hrickards/bioniscope/writeup/electronics.tex

\documentclass[12pt,a4paper]{report}

% Custom styles
\usepackage{electronics}

% Bibliography
\usepackage[citestyle=authortitle,url=true]{biblatex}
\addbibresource{electronics.bib}

\begin{document}

% Title page
\input{./tex/title.tex}

\tableofcontents
\listoffigures
%\listoftables

% Section A: Problem Analysis and Solution Design
\input{./tex/problem_analysis.tex}

% Section B: System Development
\input{./tex/system_development.tex}

% Section C: Making Measurements
\input{./tex/testing.tex}

% Section D: Evaluation and Reprot
\input{./tex/evaluation.tex}

\appendix
% Derivation of the fourier series of a square wave
\input{./tex/fourier_series_square_wave.tex}

% PIC Program Code
\input{./tex/pic_code.tex}

\listoffixmes

\printbibliography

\end{document}
