hrickards/bioniscope/circuit/alpha5/pcb_big.pdf

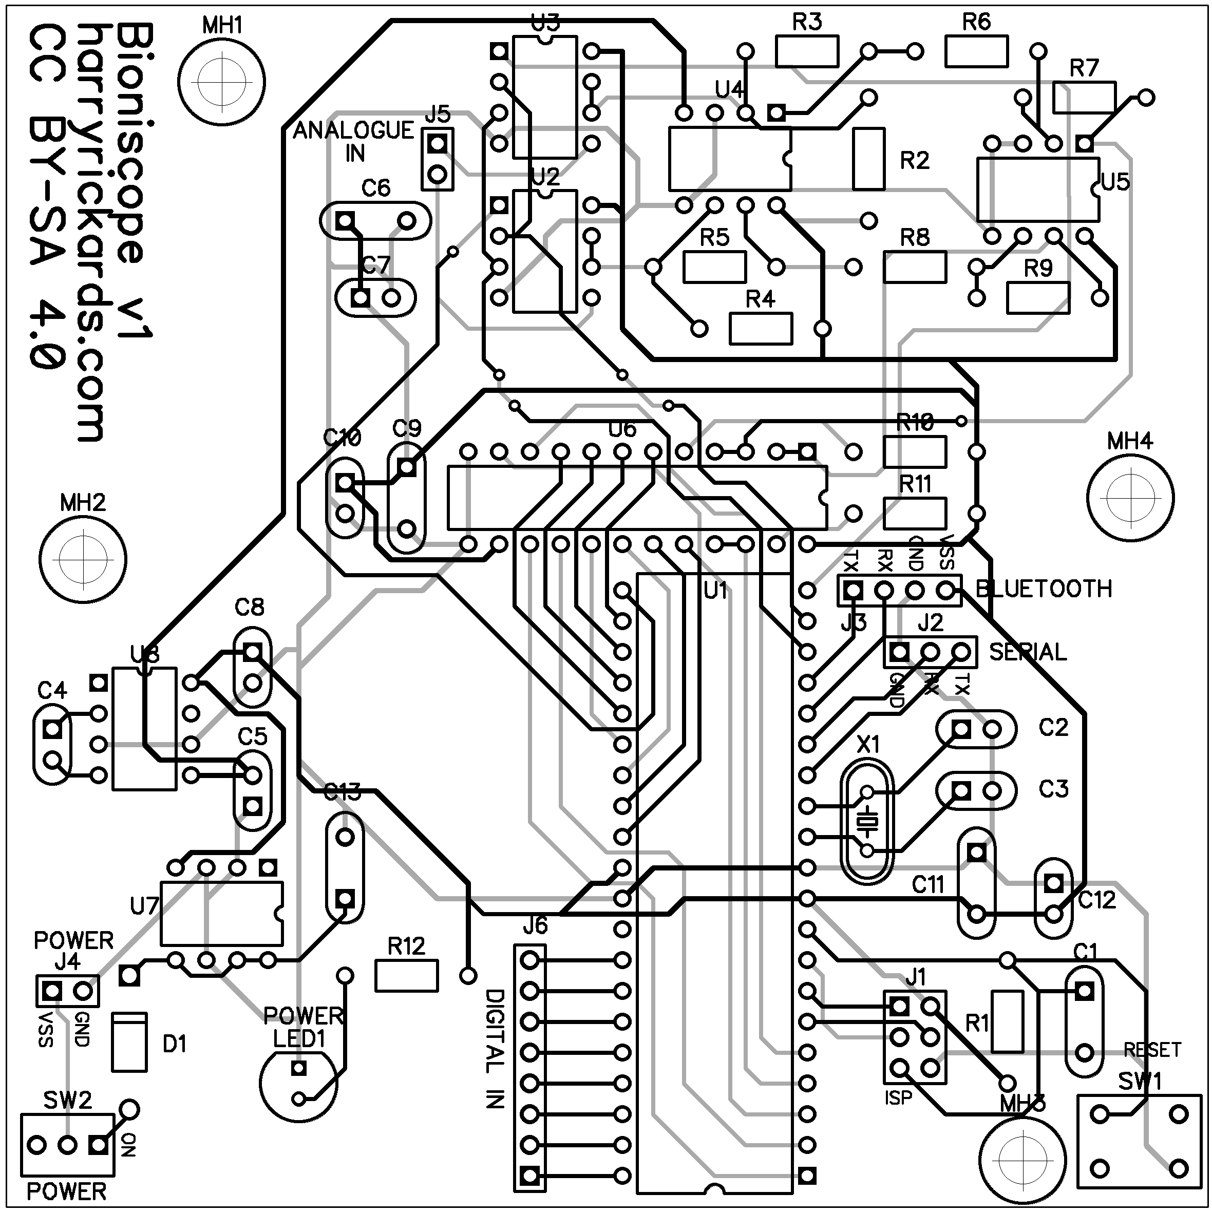
[picture p58: page 1]
