hrickards/bioniscope/writeup/img/pcb/analogue.pdf

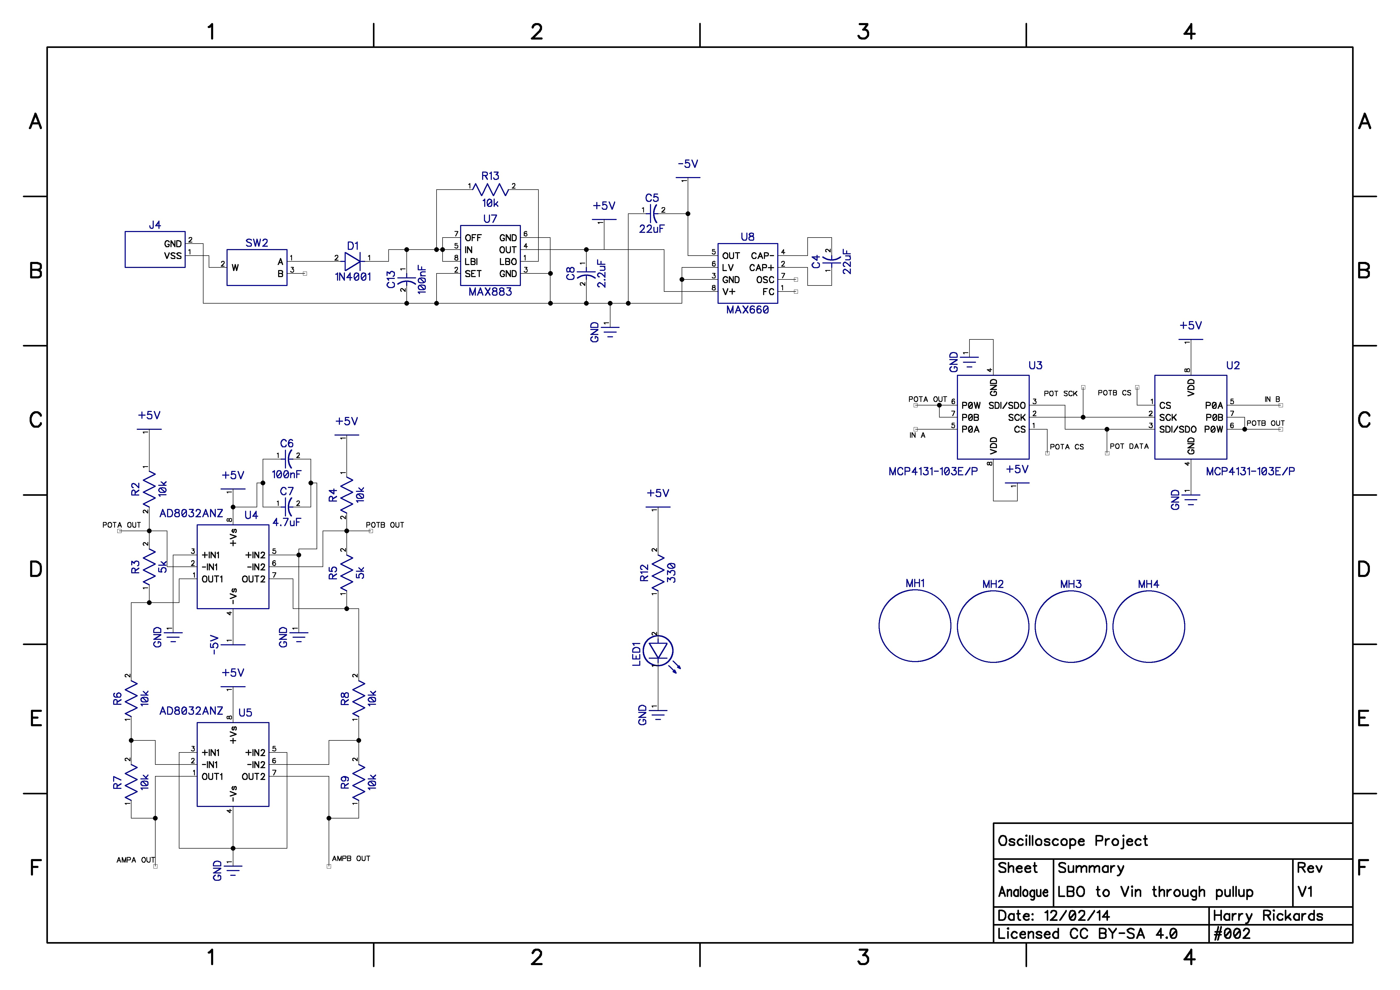
[picture p59: page 1]
