hrickards/bioniscope/writeup/img/pcb/digital.pdf

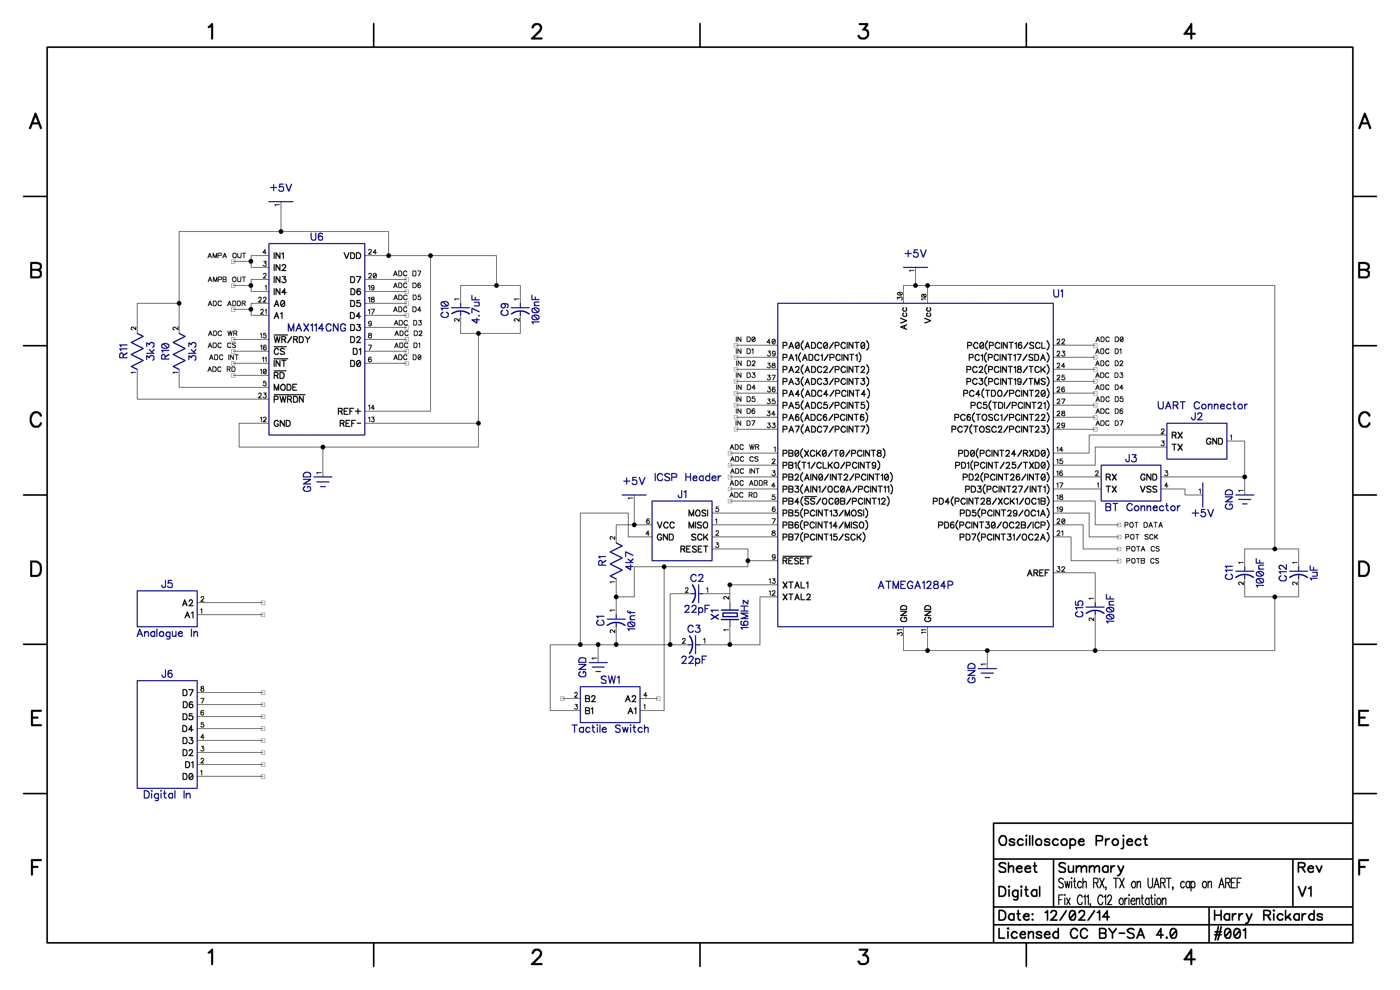
[picture p60: page 1]
