hrickards/bioniscope/circuit/alpha4/analogue.png

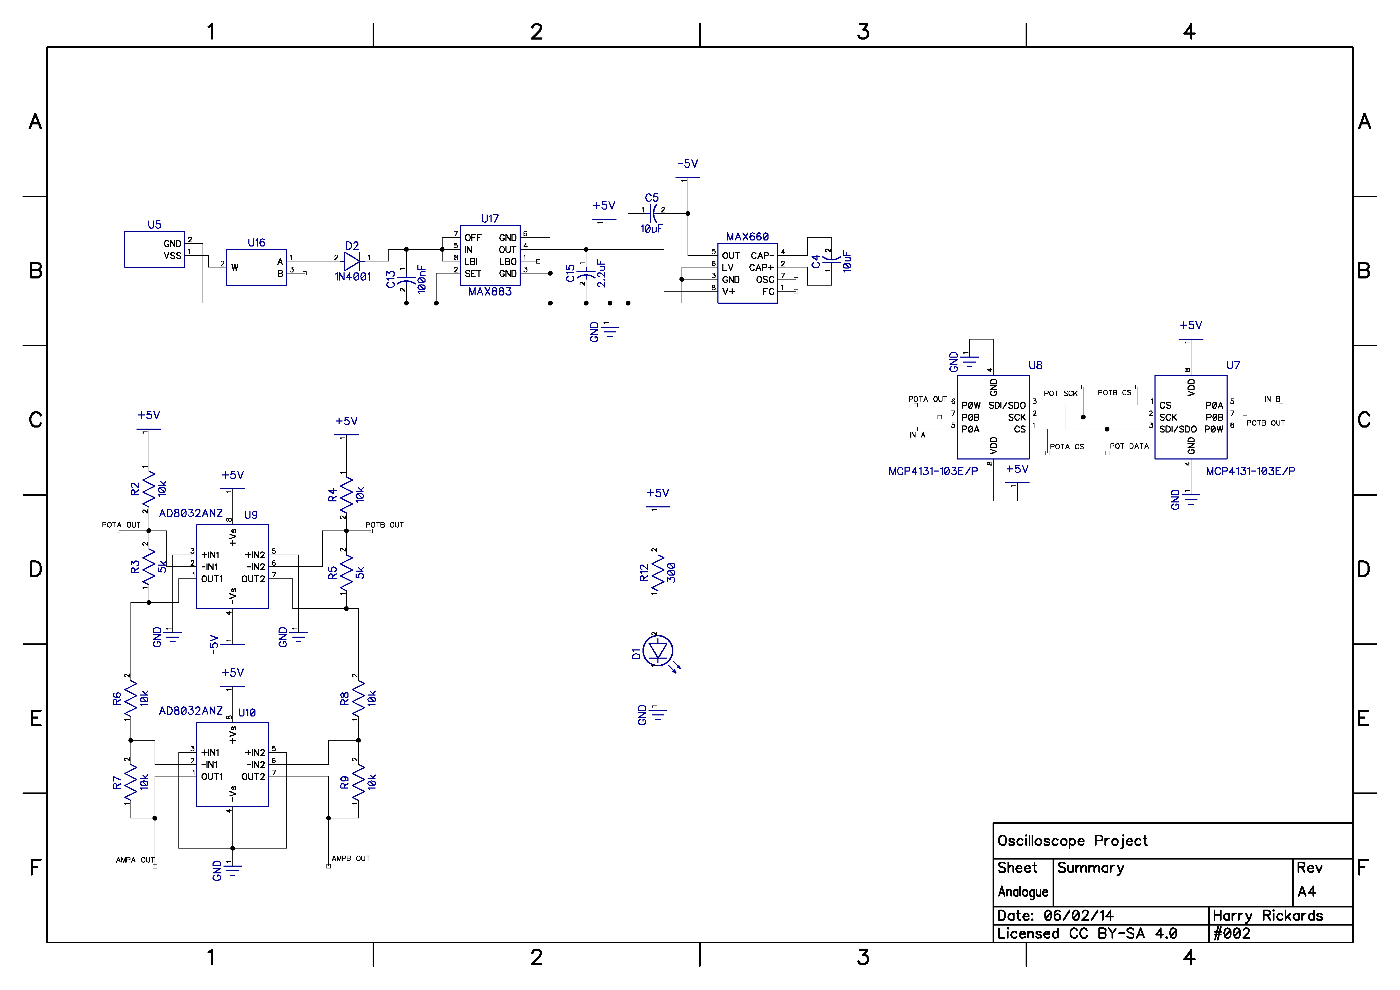
circuit/alpha4/analogue.png
