hrickards/bioniscope/circuit/alpha4/pcb_bottom.png

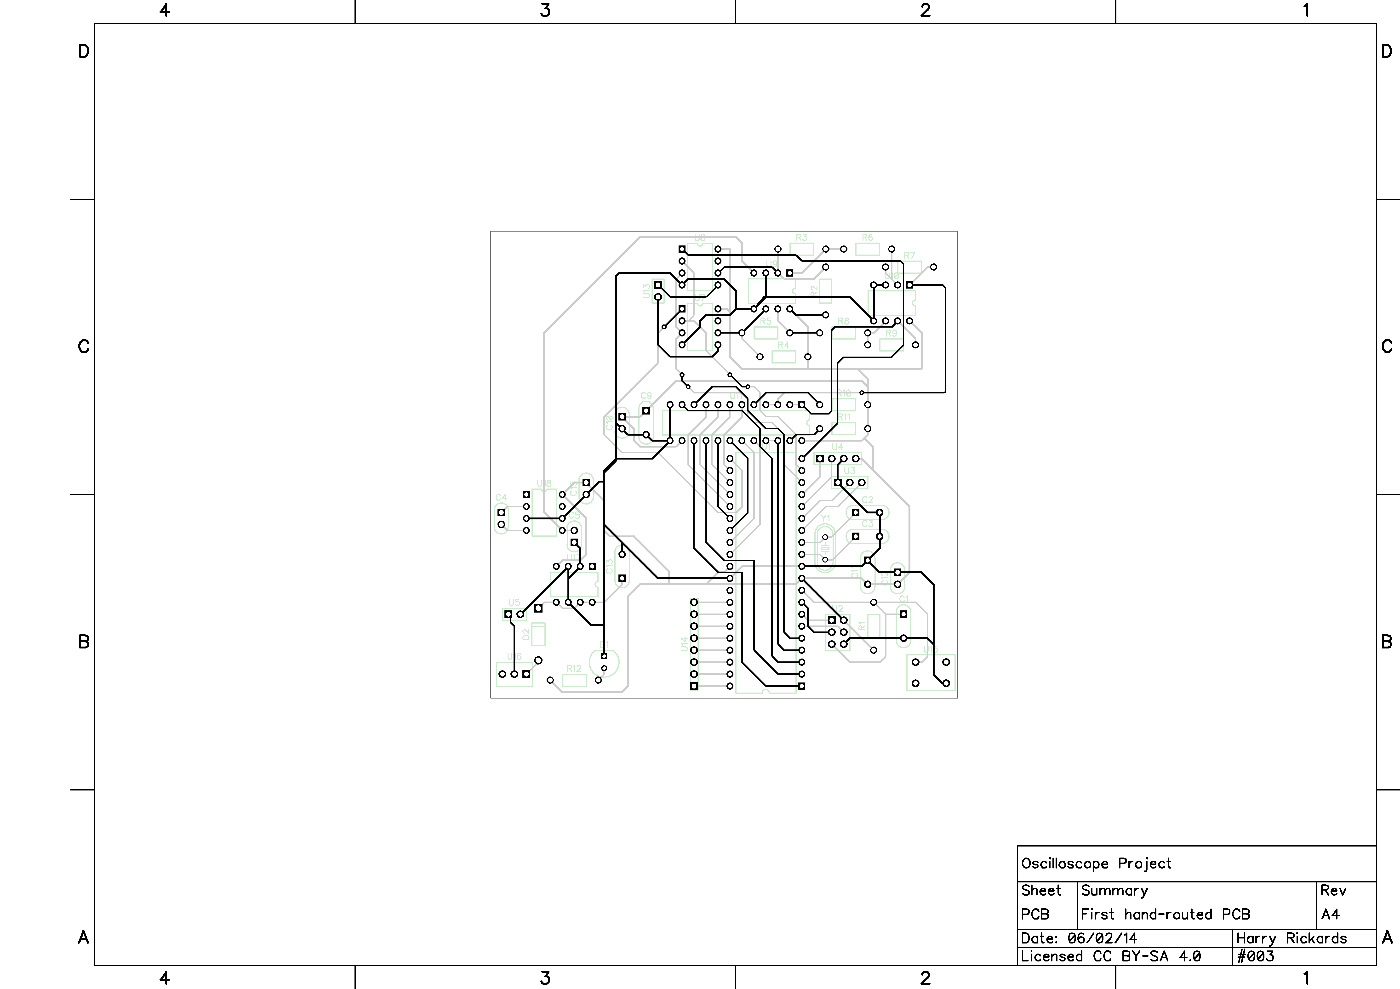
circuit/alpha4/pcb_bottom.png
