hrickards/bioniscope/circuit/alpha5/mockup/Photo 10-02-2014 10 16 06.jpg

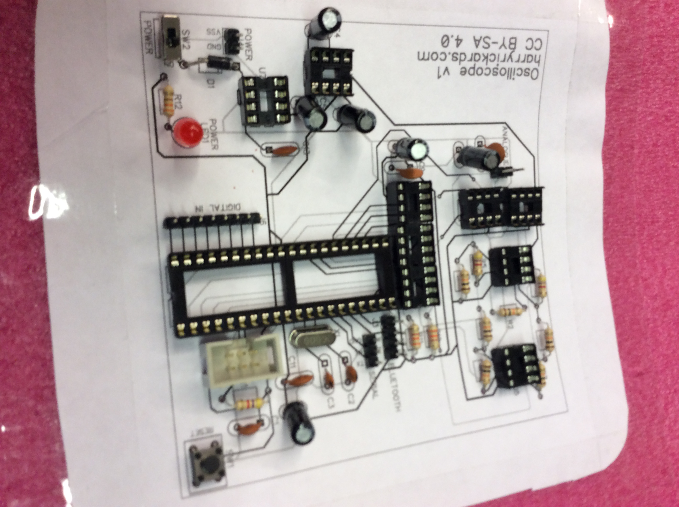
circuit/alpha5/mockup/Photo 10-02-2014 10 16 06.jpg
