hrickards/bioniscope/circuit/alpha5/mockup/Photo 10-02-2014 10 16 11 (1).jpg

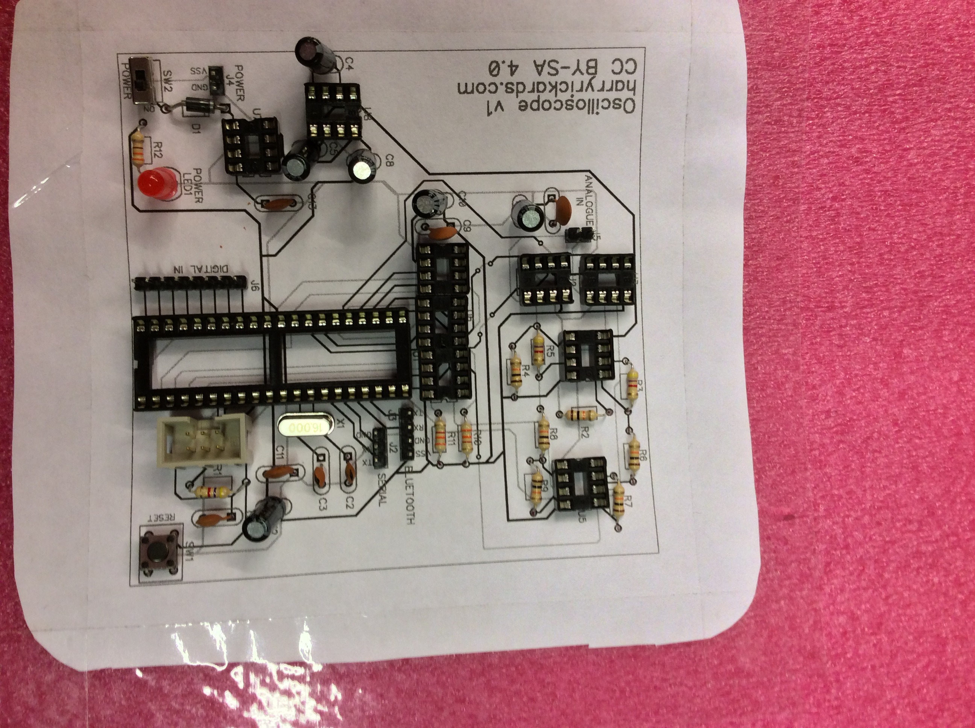
circuit/alpha5/mockup/Photo 10-02-2014 10 16 11 (1).jpg
