hrickards/bioniscope/circuit/v1/analogue.png

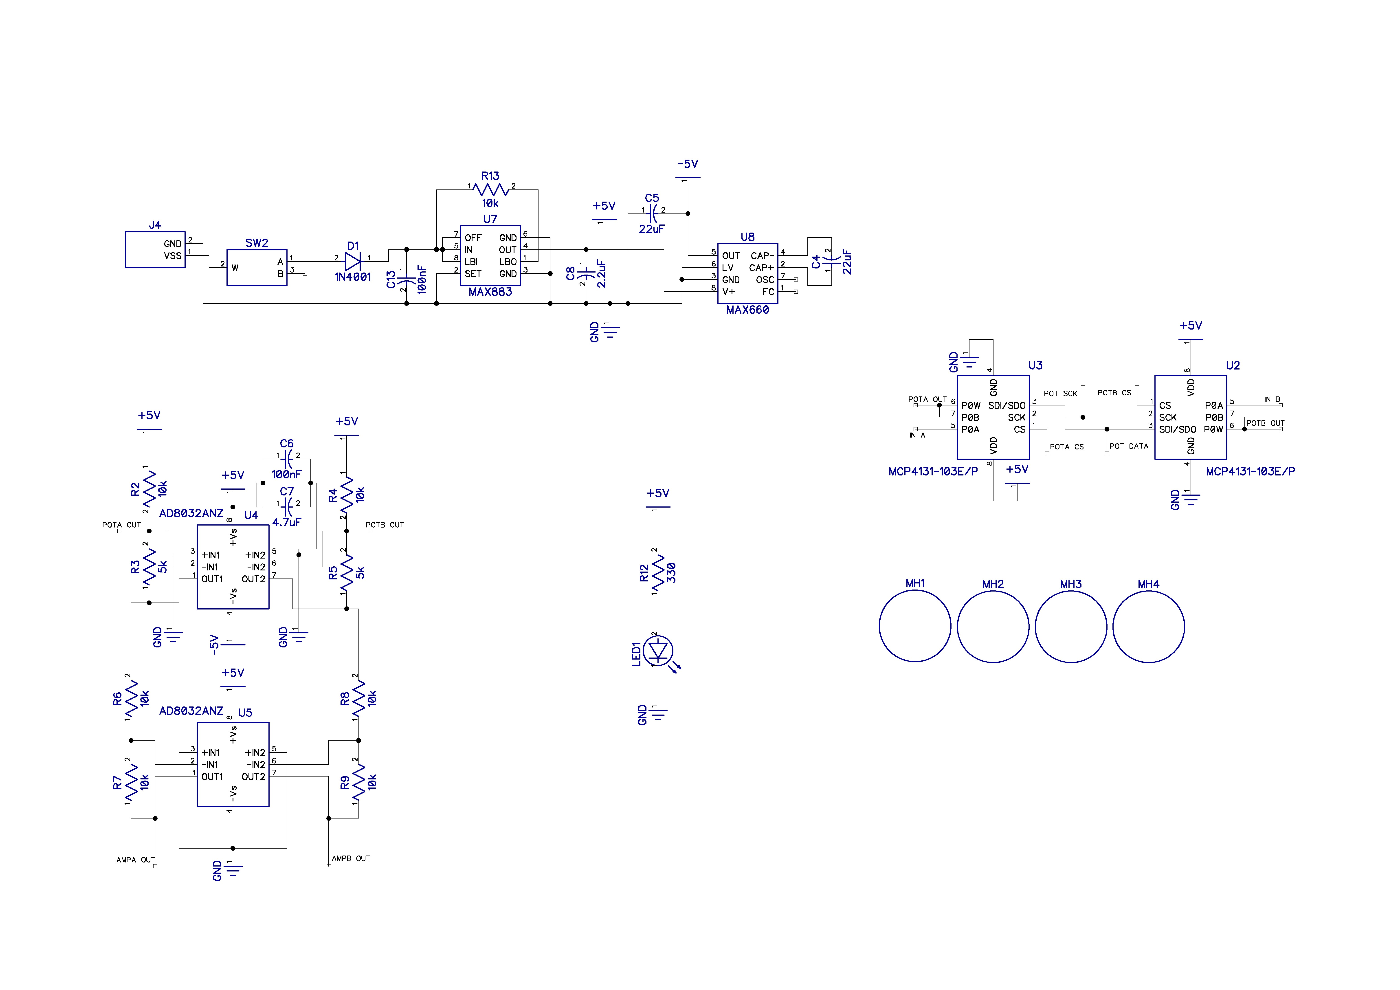
circuit/v1/analogue.png
