hrickards/bioniscope/circuit/v1/digital.png

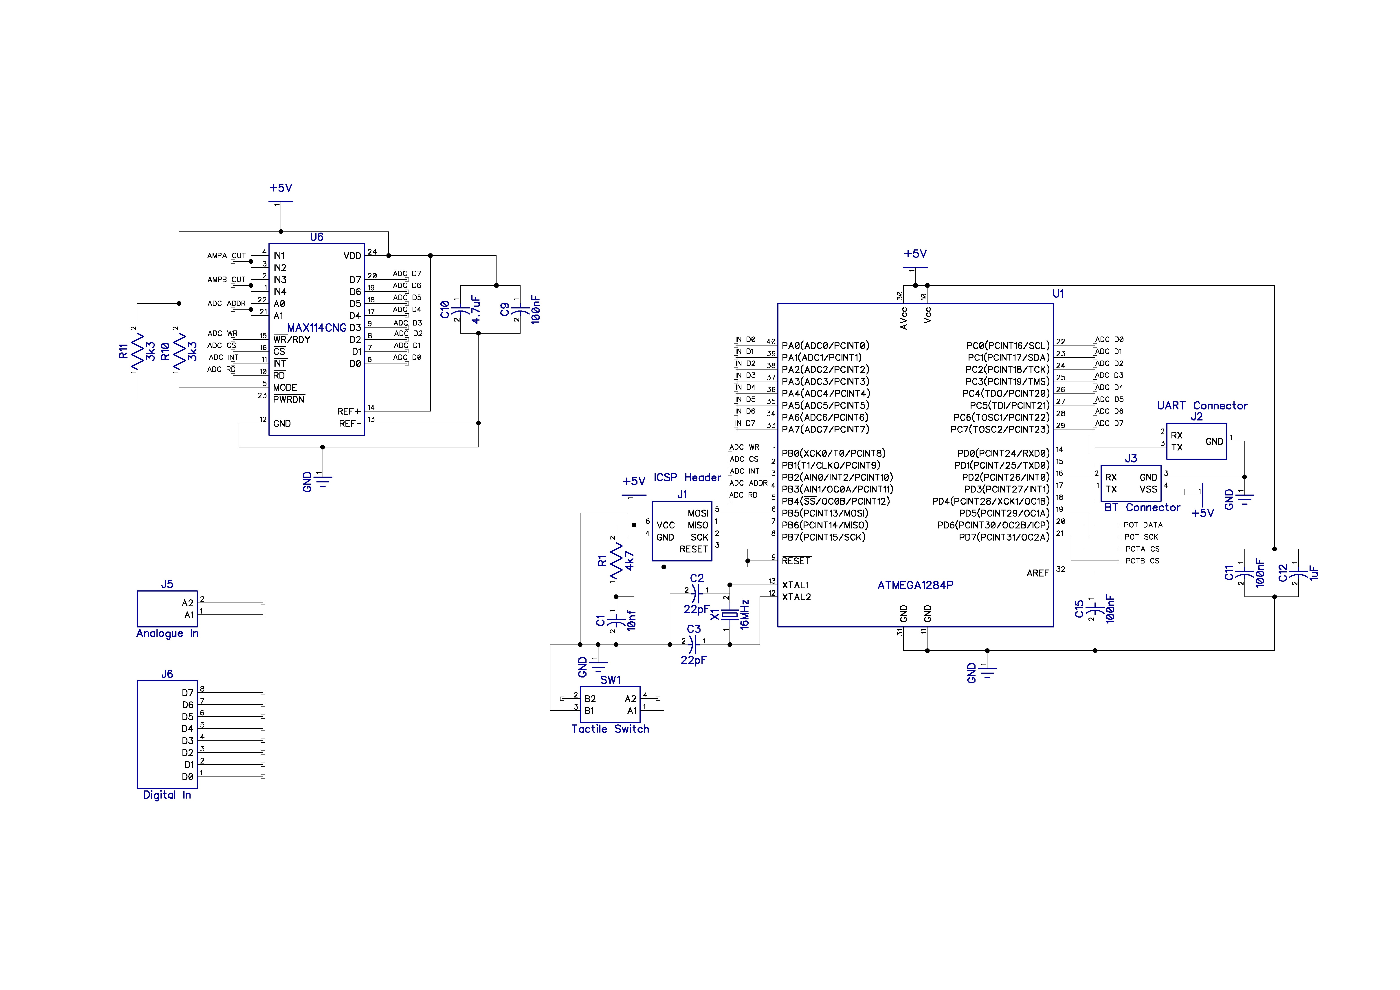
circuit/v1/digital.png
