hrickards/bioniscope/enclosure/enclosure.png

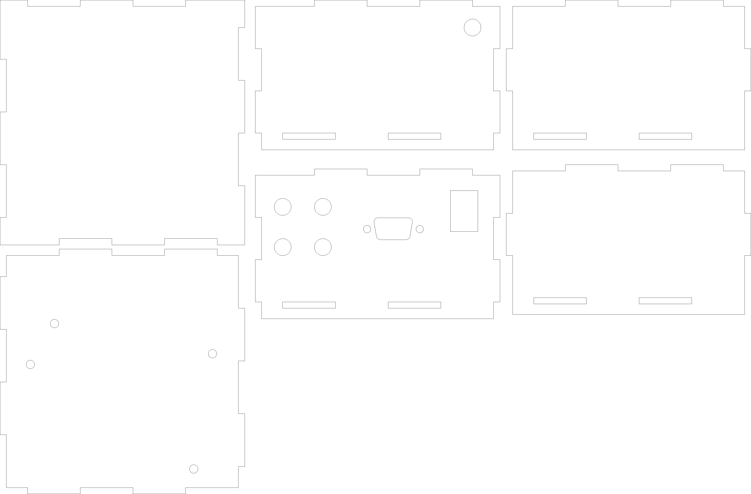
enclosure/enclosure.png
