hrickards/bioniscope/writeup/img/amplifier/circuit.png

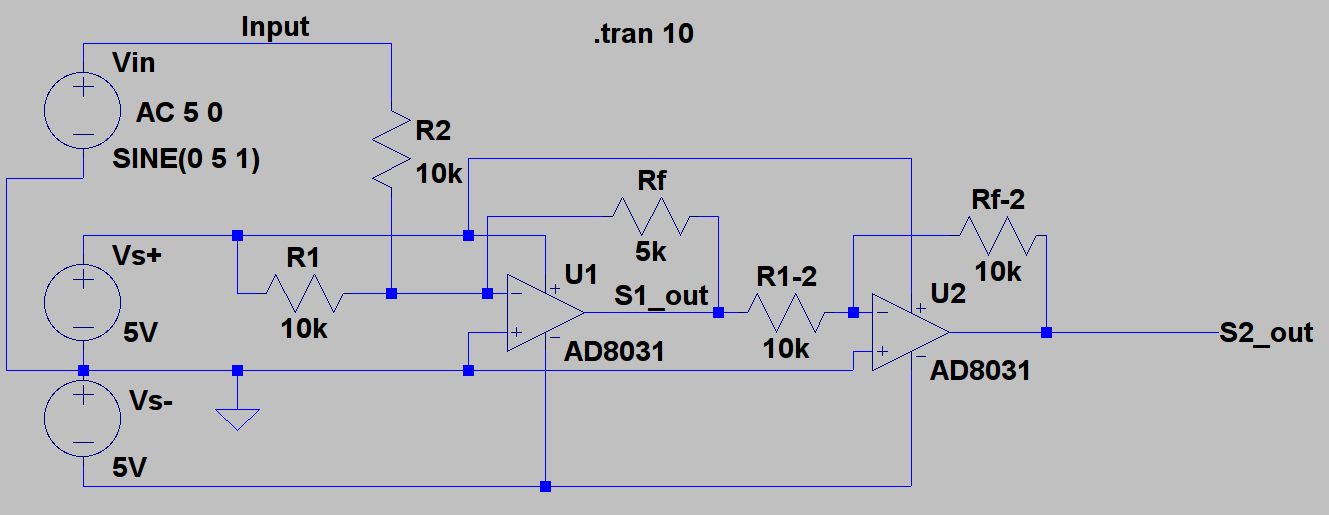
writeup/img/amplifier/circuit.png
