hrickards/bioniscope/writeup/img/amplifier/fft.png

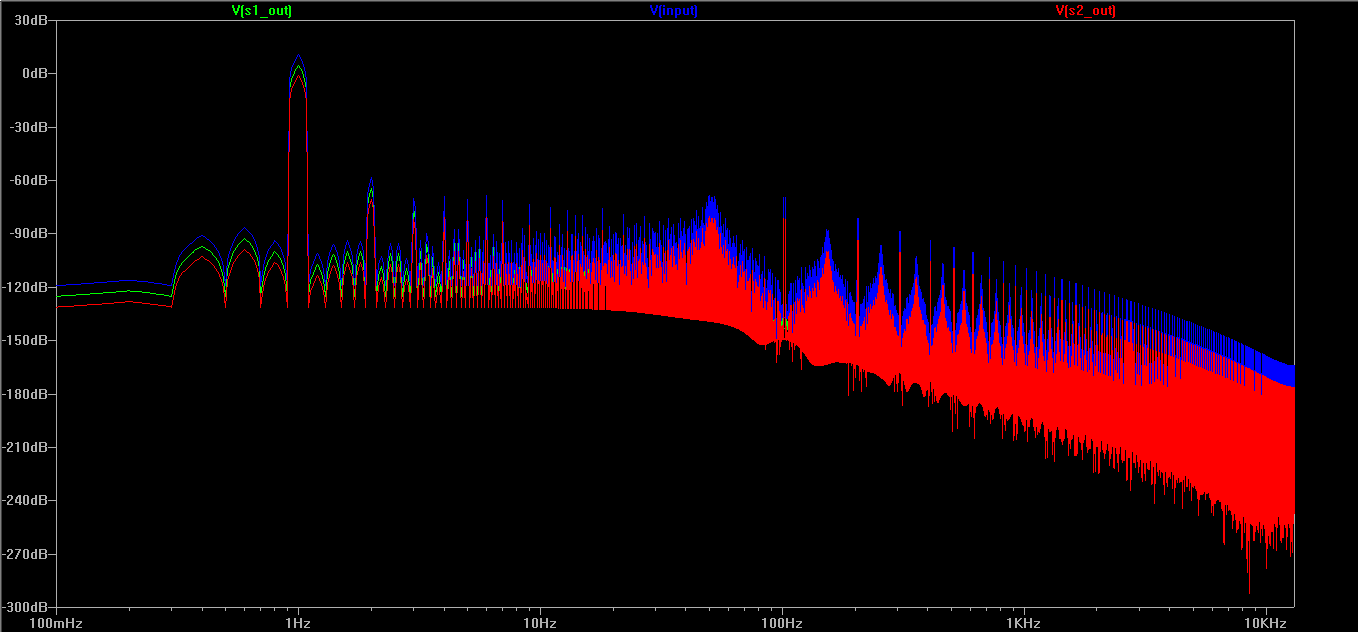
writeup/img/amplifier/fft.png
