hrickards/bioniscope/writeup/img/amplifier/frequency_response.png

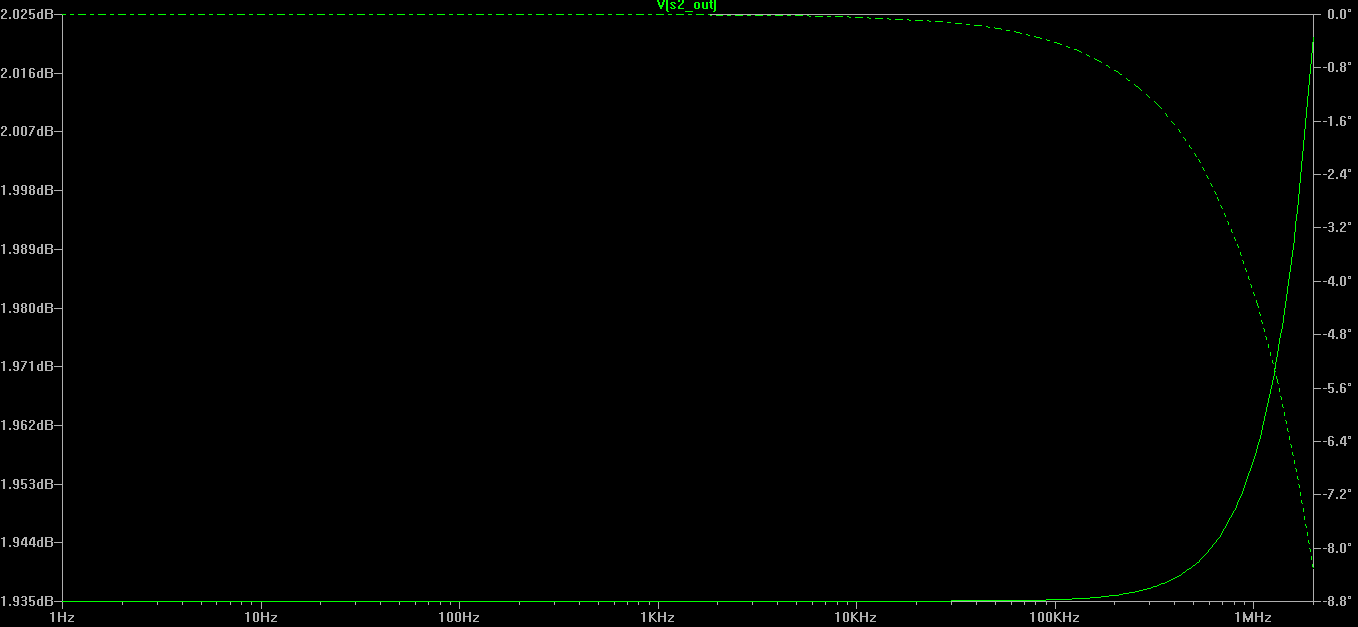
writeup/img/amplifier/frequency_response.png
