hrickards/bioniscope/writeup/img/amplifier/waveform.png

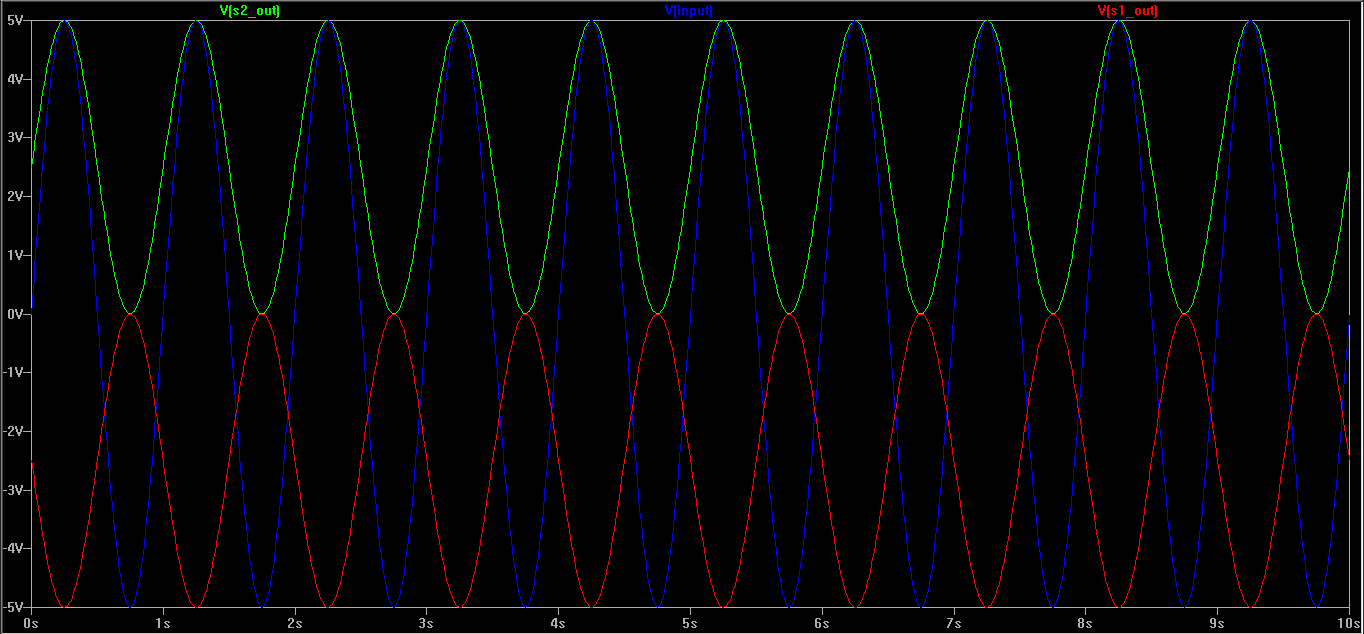
writeup/img/amplifier/waveform.png
