hrickards/bioniscope/experiments/oscilloscope/setup_02.jpg

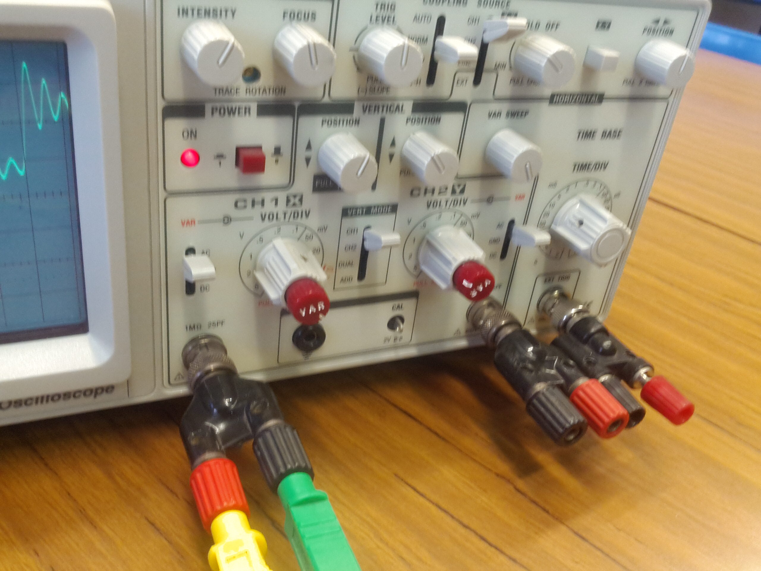
experiments/oscilloscope/setup_02.jpg
