hrickards/bioniscope/experiments/oscilloscope/setup_03.jpg

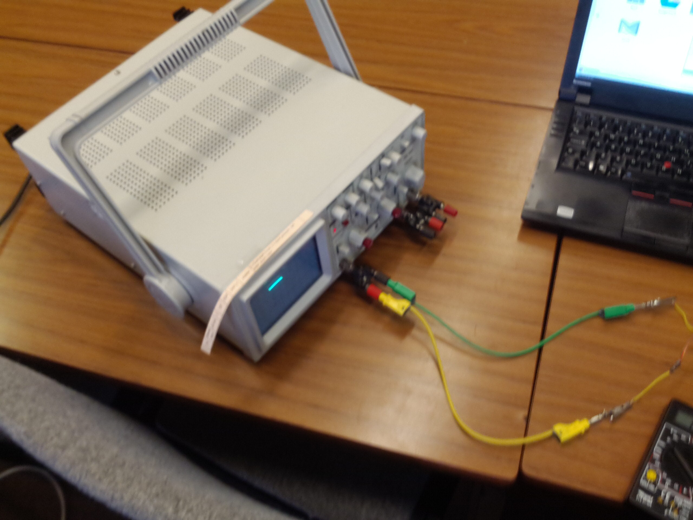
experiments/oscilloscope/setup_03.jpg
