hrickards/bioniscope/experiments/oscilloscope/setup_05.jpg

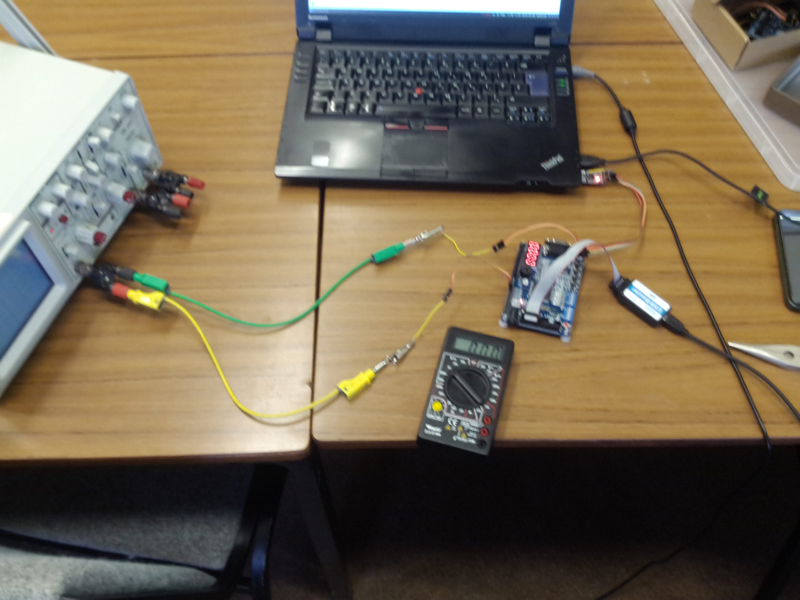
experiments/oscilloscope/setup_05.jpg
