hrickards/bioniscope/experiments/oscilloscope/setup_06.jpg

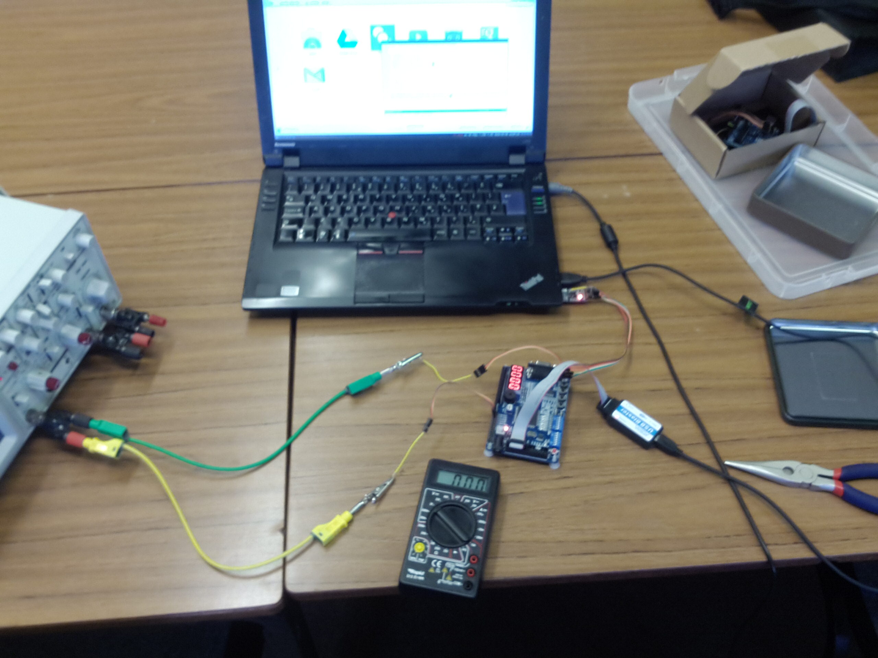
experiments/oscilloscope/setup_06.jpg
