hrickards/bioniscope/experiments/oscilloscope/setup_08.jpg

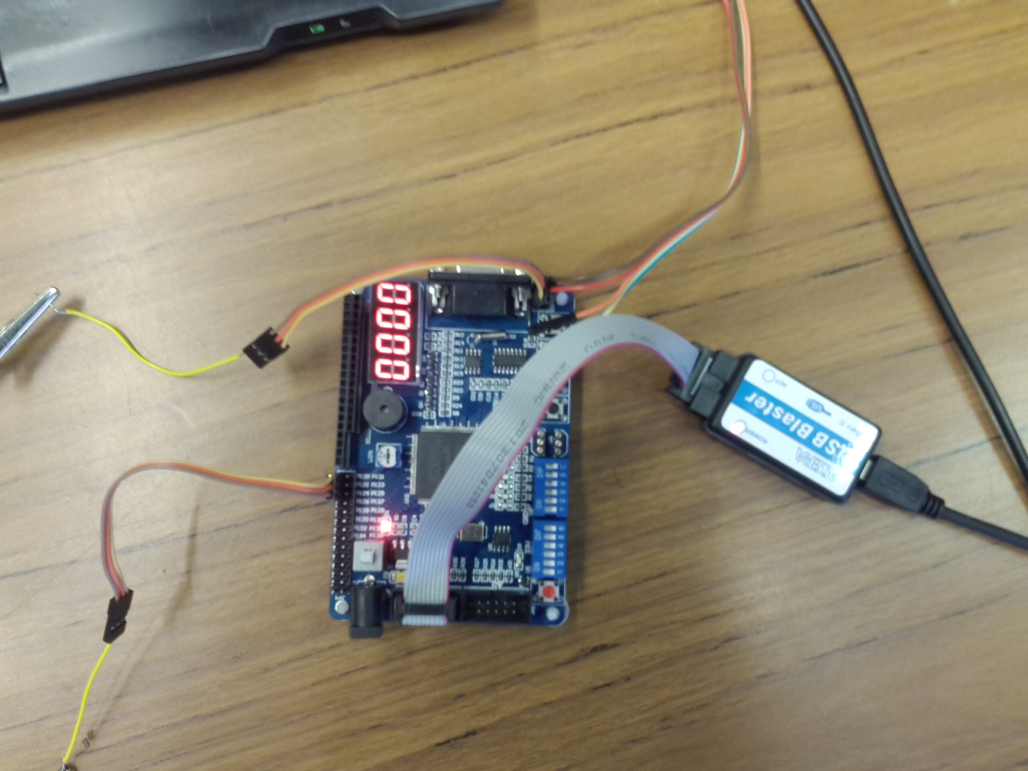
experiments/oscilloscope/setup_08.jpg
