hrickards/bioniscope/experiments/oscilloscope/setup_09.jpg

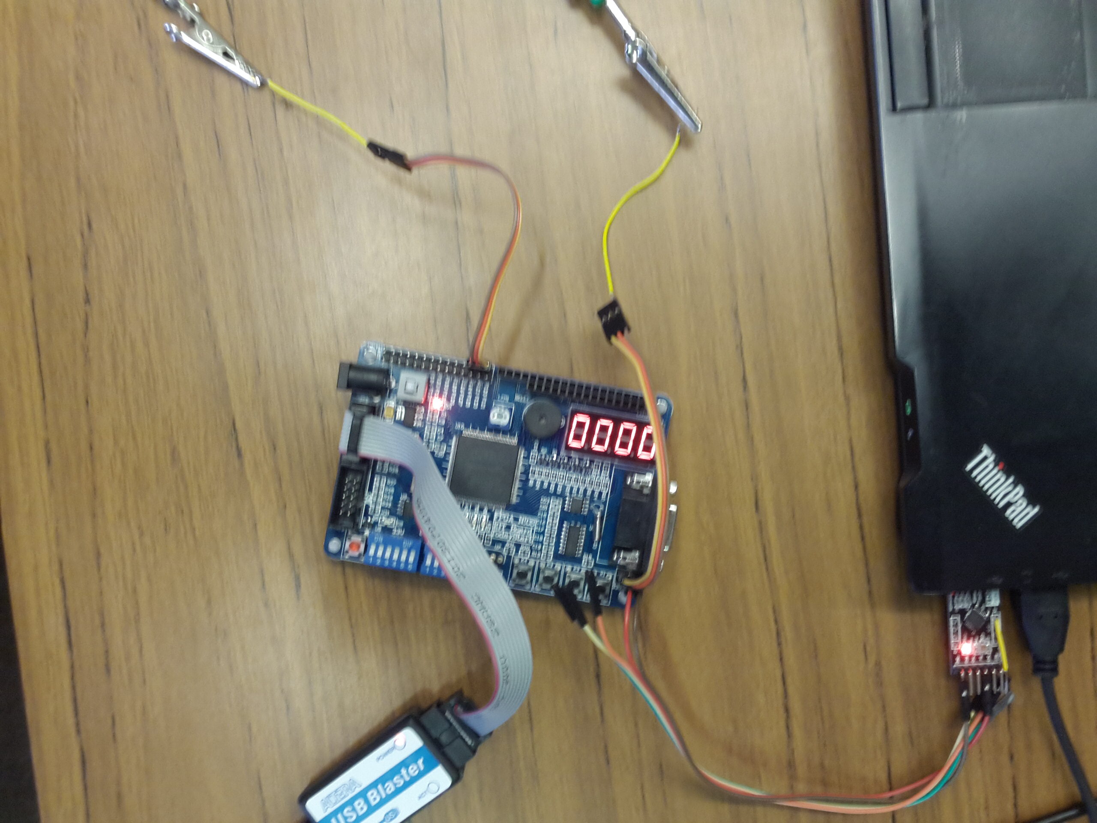
experiments/oscilloscope/setup_09.jpg
