hrickards/bioniscope/experiments/oscilloscope/setup_11.jpg

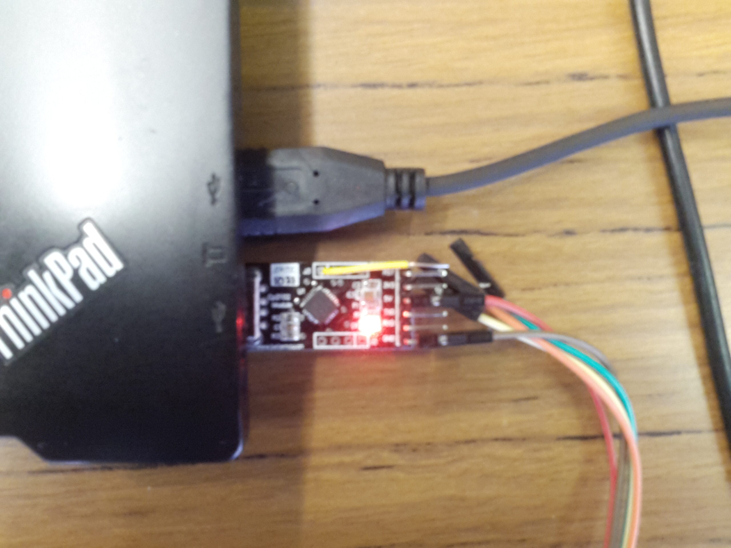
experiments/oscilloscope/setup_11.jpg
