hrickards/bioniscope/experiments/oscilloscope/setup_12.jpg

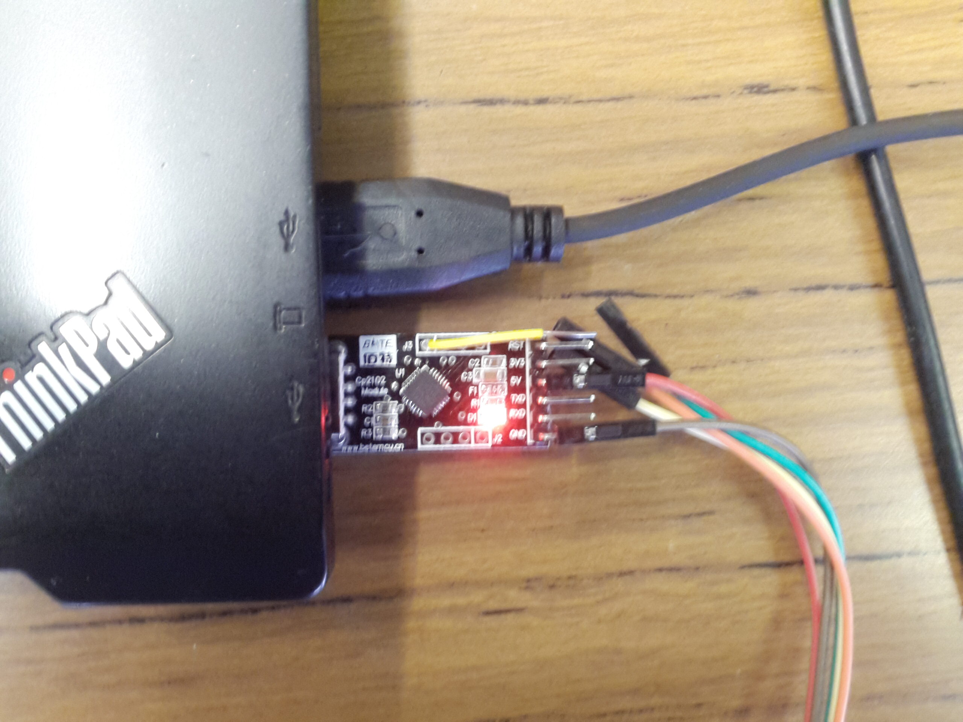
experiments/oscilloscope/setup_12.jpg
