hrickards/bioniscope/experiments/oscilloscope/setup_13.jpg

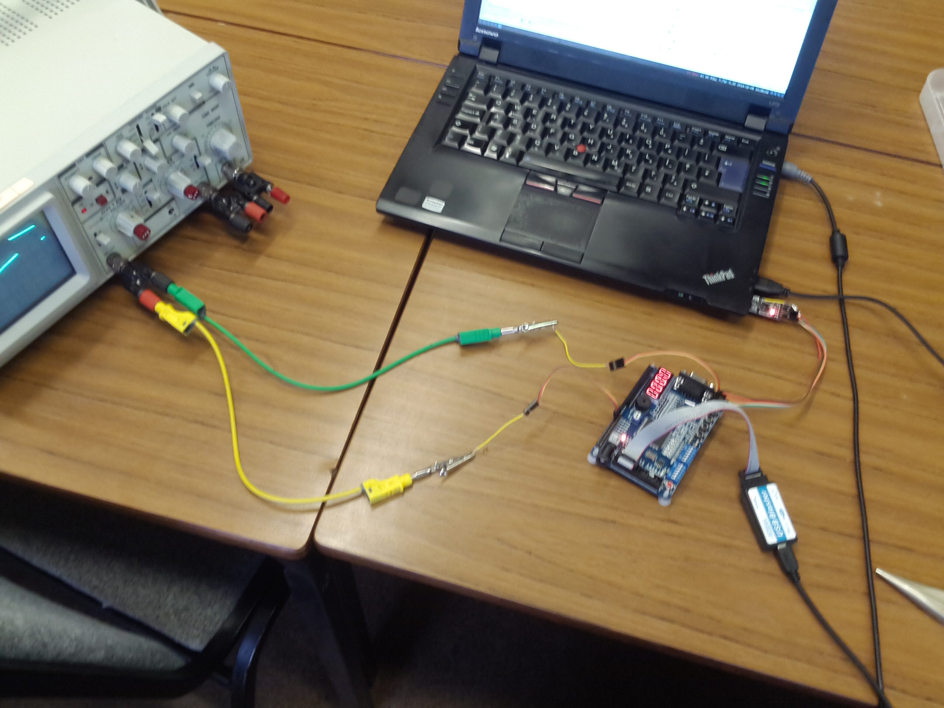
experiments/oscilloscope/setup_13.jpg
