hrickards/bioniscope/experiments/oscilloscope/measurement_05_01.jpg

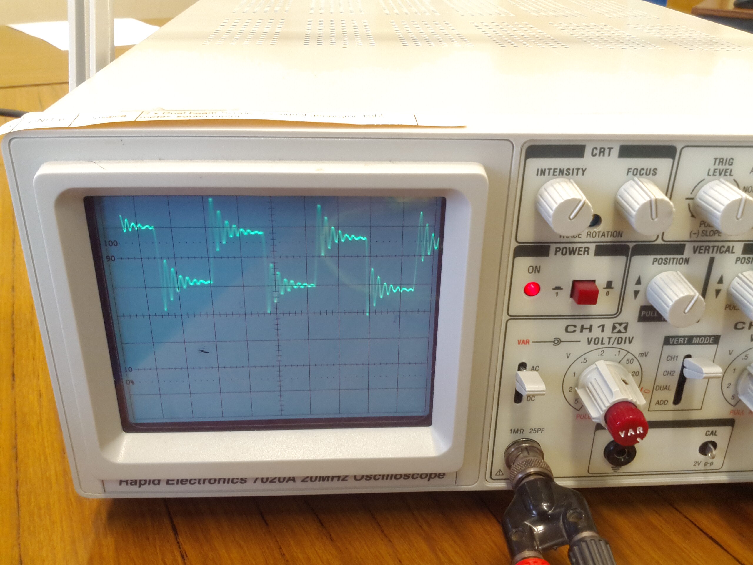
experiments/oscilloscope/measurement_05_01.jpg
