hrickards/bioniscope/experiments/oscilloscope/measurement_05_02.jpg

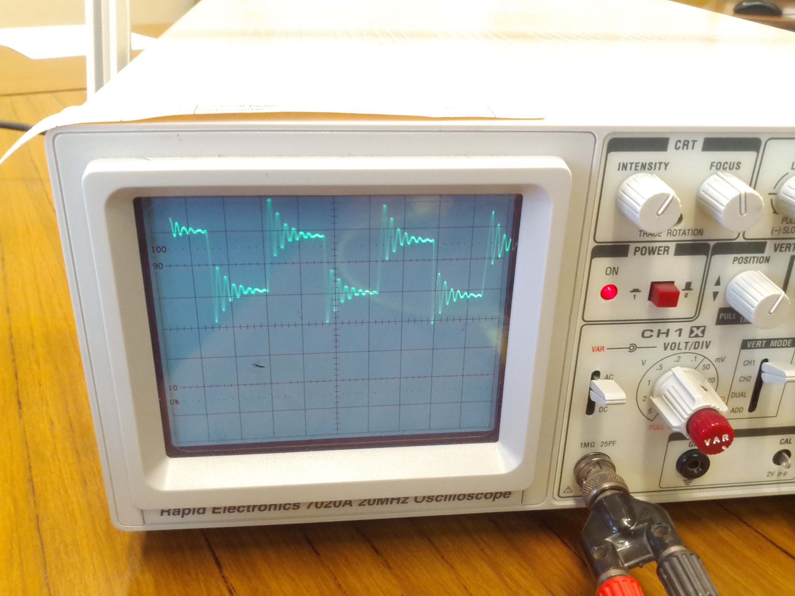
experiments/oscilloscope/measurement_05_02.jpg
