hrickards/bioniscope/experiments/oscilloscope/measurement_05_03.jpg

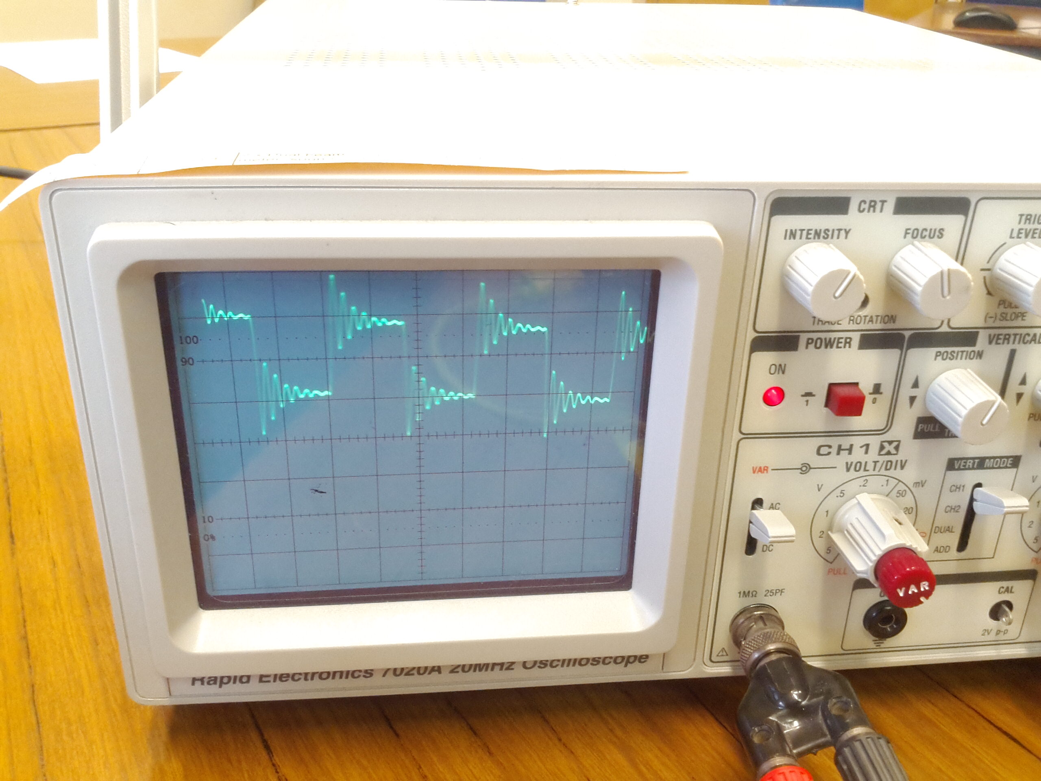
experiments/oscilloscope/measurement_05_03.jpg
