hrickards/bioniscope/experiments/oscilloscope/measurement_05_04.jpg

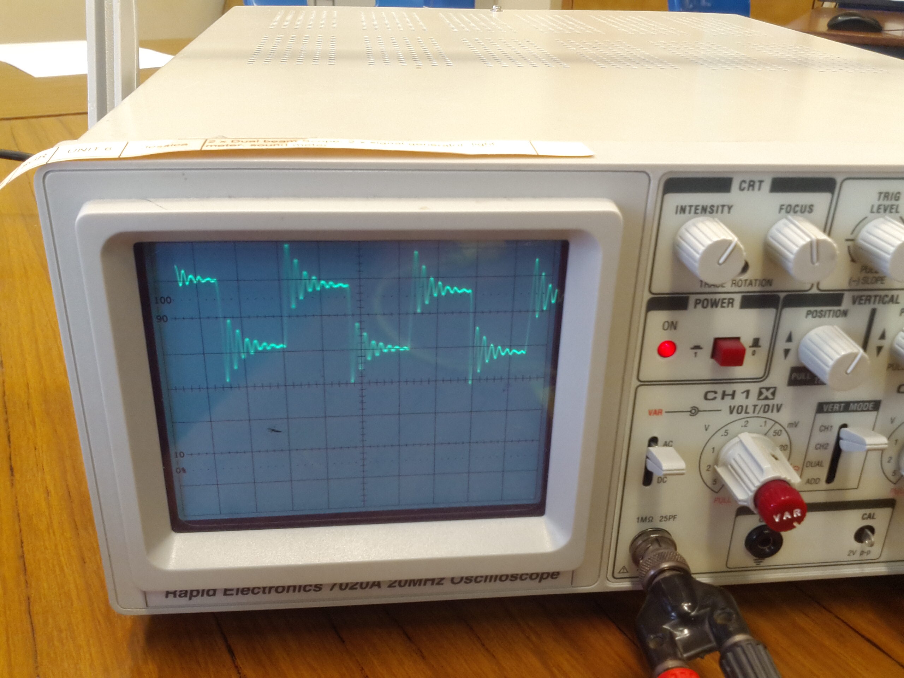
experiments/oscilloscope/measurement_05_04.jpg
