hrickards/bioniscope/experiments/oscilloscope/measurement_06_01.jpg

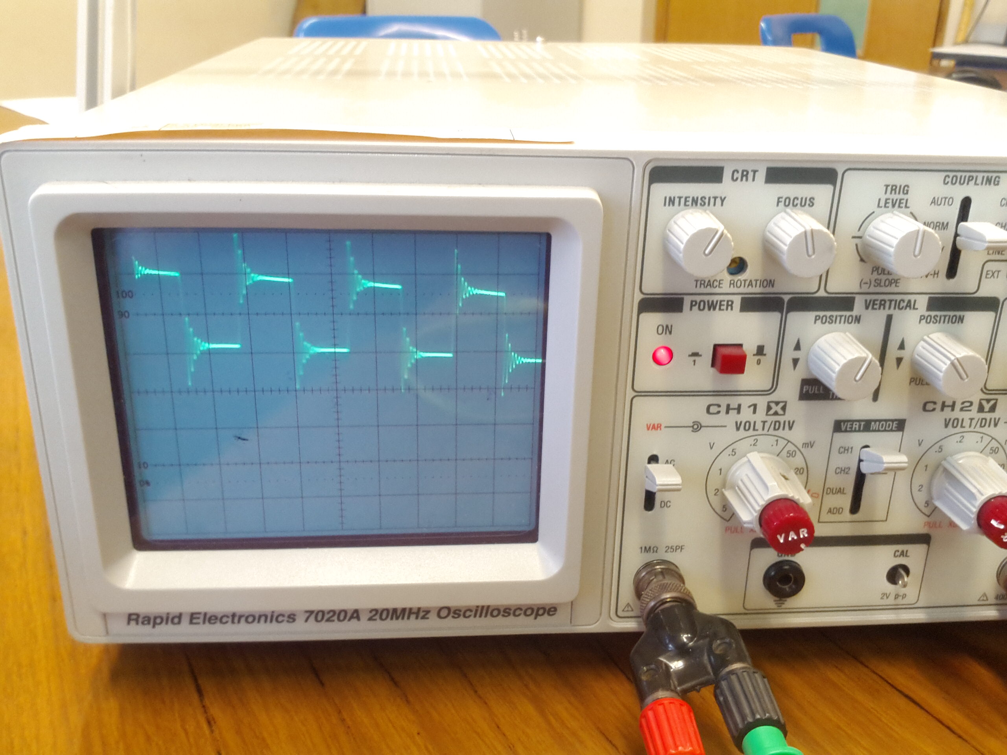
experiments/oscilloscope/measurement_06_01.jpg
