hrickards/bioniscope/experiments/oscilloscope/measurement_06_03.jpg

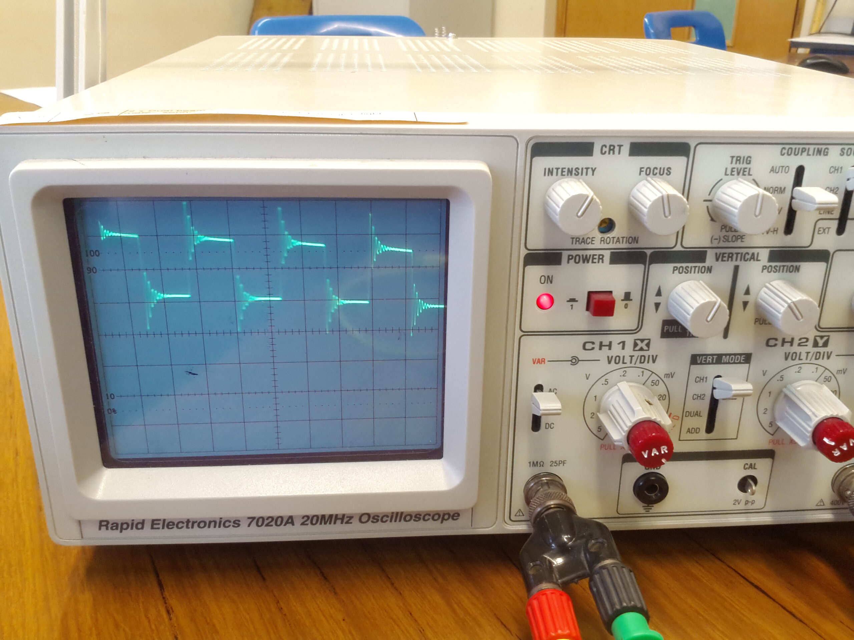
experiments/oscilloscope/measurement_06_03.jpg
