hrickards/bioniscope/experiments/oscilloscope/measurement_08_02.jpg

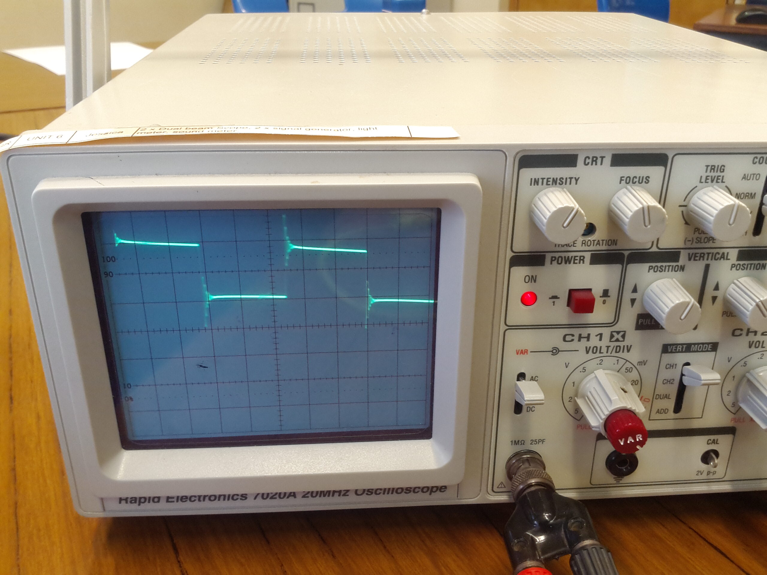
experiments/oscilloscope/measurement_08_02.jpg
