hrickards/bioniscope/experiments/oscilloscope/measurement_12_01.jpg

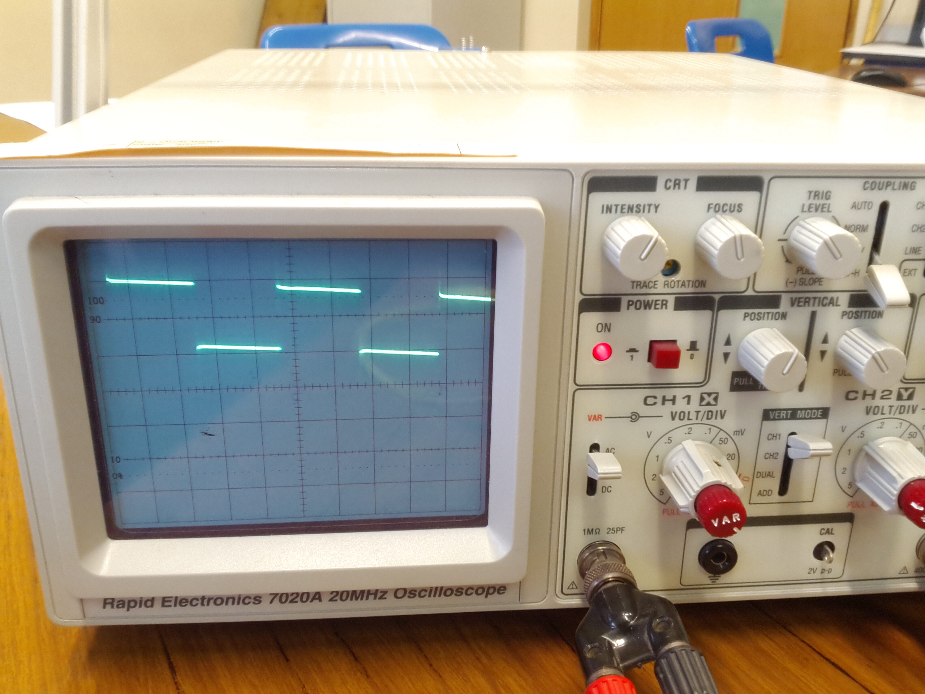
experiments/oscilloscope/measurement_12_01.jpg
