hrickards/bioniscope/experiments/oscilloscope/measurement_16_01.jpg

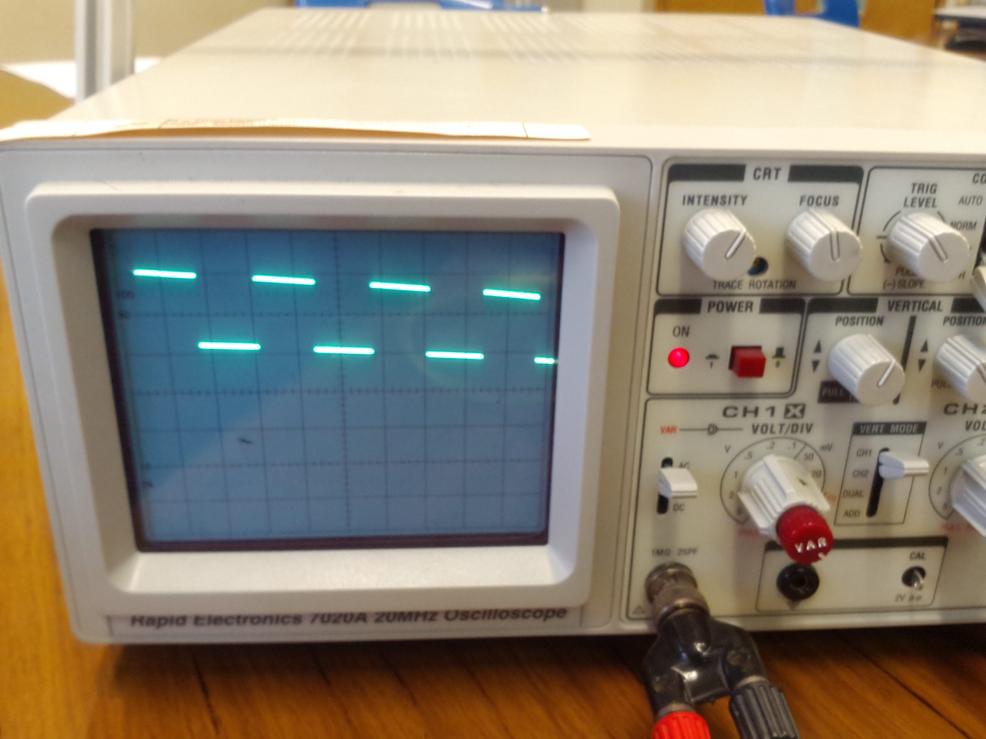
experiments/oscilloscope/measurement_16_01.jpg
