hrickards/bioniscope/experiments/oscilloscope/measurement_16_02.jpg

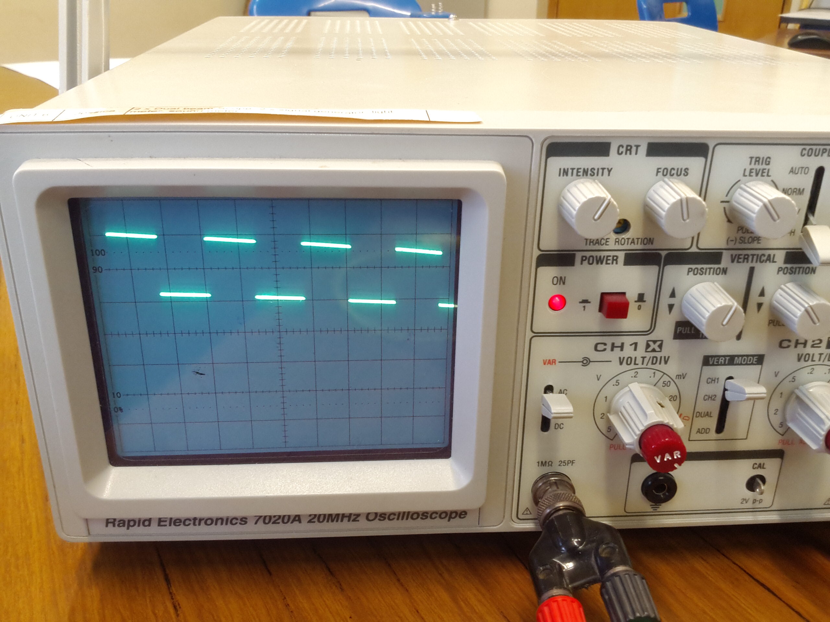
experiments/oscilloscope/measurement_16_02.jpg
