hrickards/bioniscope/simulations/amplifier.asc

R1-2: res; 10k
R1: res; 10k
R2: res; 10k
Rf-2: res; 10k
Rf: res; 5k
U1: AD8031
U2: AD8031
Vin: voltage; SINE(0 5 1); AC 5 0
Vs+: voltage; 5V
Vs-: voltage; 5V
Named nets: 0, Input, S1_out, S2_out
.tran 10
